idt12312/B-ART/firmware/src/ble_barts.c

/*
 * ble_barts.c
 *
 *  Created on: 2016/11/28
 *      Author: idt12312
 */


#include "sdk_config.h"
#include "ble_barts.h"
#include "ble_srv_common.h"
#include "sdk_common.h"


static void on_connect(ble_barts_t * p_barts, ble_evt_t * p_ble_evt)
{
    p_barts->conn_handle = p_ble_evt->evt.gap_evt.conn_handle;
}


static void on_disconnect(ble_barts_t * p_barts, ble_evt_t * p_ble_evt)
{
    UNUSED_PARAMETER(p_ble_evt);
    p_barts->conn_handle = BLE_CONN_HANDLE_INVALID;
}


static void on_write(ble_barts_t * p_barts, ble_evt_t * p_ble_evt)
{
    ble_gatts_evt_write_t * p_evt_write = &p_ble_evt->evt.gatts_evt.params.write;

    if (
        (p_evt_write->handle == p_barts->rx_handles.cccd_handle)
        &&
        (p_evt_write->len == 2)
       )
    {
        if (ble_srv_is_notification_enabled(p_evt_write->data))
        {
            p_barts->is_notification_enabled = true;
        }
        else
        {
            p_barts->is_notification_enabled = false;
        }
    }
    else if (
             (p_evt_write->handle == p_barts->tx_handles.value_handle)
             &&
             (p_barts->data_handler != NULL)
            )
    {
        p_barts->data_handler(p_barts, p_evt_write->data, p_evt_write->len);
    }
    else
    {
        // Do Nothing. This event is not relevant for this service.
    }
}


static uint32_t rx_char_add(ble_barts_t * p_barts, const ble_barts_init_t * p_barts_init)
{
    /**@snippet [Adding proprietary characteristic to S110 SoftDevice] */
    ble_gatts_char_md_t char_md;
    ble_gatts_attr_md_t cccd_md;
    ble_gatts_attr_t    attr_char_value;
    ble_uuid_t          ble_uuid;
    ble_gatts_attr_md_t attr_md;

    memset(&cccd_md, 0, sizeof(cccd_md));

    BLE_GAP_CONN_SEC_MODE_SET_OPEN(&cccd_md.read_perm);
    BLE_GAP_CONN_SEC_MODE_SET_OPEN(&cccd_md.write_perm);

    cccd_md.vloc = BLE_GATTS_VLOC_STACK;

    memset(&char_md, 0, sizeof(char_md));

    char_md.char_props.notify = 1;
    char_md.p_char_user_desc  = NULL;
    char_md.p_char_pf         = NULL;
    char_md.p_user_desc_md    = NULL;
    char_md.p_cccd_md         = &cccd_md;
    char_md.p_sccd_md         = NULL;

    ble_uuid.type = p_barts->uuid_type;
    ble_uuid.uuid = BLE_UUID_BARTS_RX_CHARACTERISTIC;

    memset(&attr_md, 0, sizeof(attr_md));

    BLE_GAP_CONN_SEC_MODE_SET_OPEN(&attr_md.read_perm);
    BLE_GAP_CONN_SEC_MODE_SET_OPEN(&attr_md.write_perm);

    attr_md.vloc    = BLE_GATTS_VLOC_STACK;
    attr_md.rd_auth = 0;
    attr_md.wr_auth = 0;
    attr_md.vlen    = 1;

    memset(&attr_char_value, 0, sizeof(attr_char_value));

    attr_char_value.p_uuid    = &ble_uuid;
    attr_char_value.p_attr_md = &attr_md;
    attr_char_value.init_len  = sizeof(uint8_t);
    attr_char_value.init_offs = 0;
    attr_char_value.max_len   = BLE_BARTS_MAX_RX_CHAR_LEN;

    return sd_ble_gatts_characteristic_add(p_barts->service_handle,
                                           &char_md,
                                           &attr_char_value,
                                           &p_barts->rx_handles);
    /**@snippet [Adding proprietary characteristic to S110 SoftDevice] */
}


static uint32_t tx_char_add(ble_barts_t * p_barts, const ble_barts_init_t * p_barts_init)
{
    ble_gatts_char_md_t char_md;
    ble_gatts_attr_t    attr_char_value;
    ble_uuid_t          ble_uuid;
    ble_gatts_attr_md_t attr_md;

    memset(&char_md, 0, sizeof(char_md));

    char_md.char_props.write         = 1;
    char_md.char_props.write_wo_resp = 1;
    char_md.p_char_user_desc         = NULL;
    char_md.p_char_pf                = NULL;
    char_md.p_user_desc_md           = NULL;
    char_md.p_cccd_md                = NULL;
    char_md.p_sccd_md                = NULL;

    ble_uuid.type = p_barts->uuid_type;
    ble_uuid.uuid = BLE_UUID_BARTS_TX_CHARACTERISTIC;

    memset(&attr_md, 0, sizeof(attr_md));

    BLE_GAP_CONN_SEC_MODE_SET_OPEN(&attr_md.read_perm);
    BLE_GAP_CONN_SEC_MODE_SET_OPEN(&attr_md.write_perm);

    attr_md.vloc    = BLE_GATTS_VLOC_STACK;
    attr_md.rd_auth = 0;
    attr_md.wr_auth = 0;
    attr_md.vlen    = 1;

    memset(&attr_char_value, 0, sizeof(attr_char_value));

    attr_char_value.p_uuid    = &ble_uuid;
    attr_char_value.p_attr_md = &attr_md;
    attr_char_value.init_len  = 1;
    attr_char_value.init_offs = 0;
    attr_char_value.max_len   = BLE_BARTS_MAX_TX_CHAR_LEN;

    return sd_ble_gatts_characteristic_add(p_barts->service_handle,
                                           &char_md,
                                           &attr_char_value,
                                           &p_barts->tx_handles);
}


void ble_barts_on_ble_evt(ble_barts_t * p_barts, ble_evt_t * p_ble_evt)
{
    if ((p_barts == NULL) || (p_ble_evt == NULL))
    {
        return;
    }

    switch (p_ble_evt->header.evt_id)
    {
        case BLE_GAP_EVT_CONNECTED:
            on_connect(p_barts, p_ble_evt);
            break;

        case BLE_GAP_EVT_DISCONNECTED:
            on_disconnect(p_barts, p_ble_evt);
            break;

        case BLE_GATTS_EVT_WRITE:
            on_write(p_barts, p_ble_evt);
            break;

        default:
            // No implementation needed.
            break;
    }
}


uint32_t ble_barts_init(ble_barts_t * p_barts, const ble_barts_init_t * p_barts_init)
{
    uint32_t      err_code;
    ble_uuid_t    ble_uuid;
    ble_uuid128_t barts_base_uuid = BARTS_BASE_UUID;

    // device id をUUIDに埋め込み
    barts_base_uuid.uuid128[14] = p_barts_init->device_id;

    VERIFY_PARAM_NOT_NULL(p_barts);
    VERIFY_PARAM_NOT_NULL(p_barts_init);

    // Initialize the service structure.
    p_barts->conn_handle             = BLE_CONN_HANDLE_INVALID;
    p_barts->data_handler            = p_barts_init->data_handler;
    p_barts->is_notification_enabled = false;

    /**@snippet [Adding proprietary Service to S110 SoftDevice] */
    // Add a custom base UUID.
    err_code = sd_ble_uuid_vs_add(&barts_base_uuid, &p_barts->uuid_type);
    VERIFY_SUCCESS(err_code);

    ble_uuid.type = p_barts->uuid_type;
    ble_uuid.uuid = BLE_UUID_BARTS_SERVICE;

    // Add the service.
    err_code = sd_ble_gatts_service_add(BLE_GATTS_SRVC_TYPE_PRIMARY,
                                        &ble_uuid,
                                        &p_barts->service_handle);
    /**@snippet [Adding proprietary Service to S110 SoftDevice] */
    VERIFY_SUCCESS(err_code);

    // Add the RX Characteristic.
    err_code = rx_char_add(p_barts, p_barts_init);
    VERIFY_SUCCESS(err_code);

    // Add the TX Characteristic.
    err_code = tx_char_add(p_barts, p_barts_init);
    VERIFY_SUCCESS(err_code);

    return NRF_SUCCESS;
}


uint32_t ble_barts_send(ble_barts_t * p_barts, uint8_t * p_data, uint16_t length)
{
    ble_gatts_hvx_params_t hvx_params;

    VERIFY_PARAM_NOT_NULL(p_barts);

    if ((p_barts->conn_handle == BLE_CONN_HANDLE_INVALID) || (!p_barts->is_notification_enabled))
    {
        return NRF_ERROR_INVALID_STATE;
    }

    if (length > BLE_BARTS_MAX_DATA_LEN)
    {
        return NRF_ERROR_INVALID_PARAM;
    }

    memset(&hvx_params, 0, sizeof(hvx_params));

    hvx_params.handle = p_barts->rx_handles.value_handle;
    hvx_params.p_data = p_data;
    hvx_params.p_len  = &length;
    hvx_params.type   = BLE_GATT_HVX_NOTIFICATION;

    return sd_ble_gatts_hvx(p_barts->conn_handle, &hvx_params);
}
